majaczech/wind-tunnel/wiring/Flow-regulator.PNG

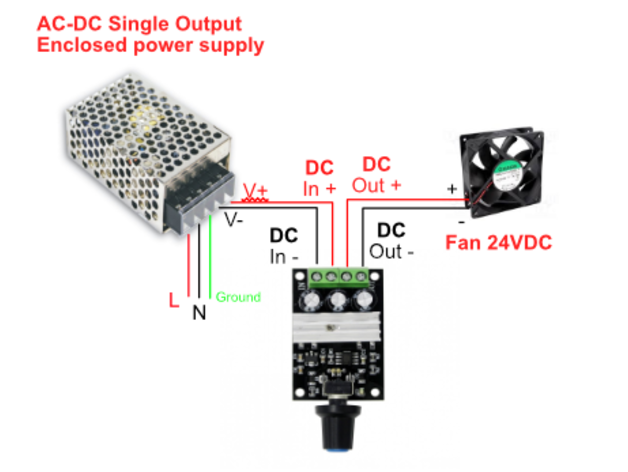
wiring/Flow-regulator.PNG
