majaczech/wind-tunnel/wiring/hot-wire.jpg

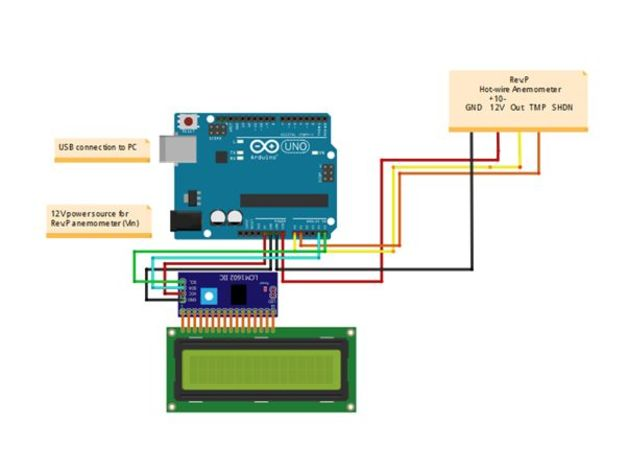
wiring/hot-wire.jpg
